kiu/eAVR/eAVR6-adapter-hrz/eAVR6-adapter-hrz2.png

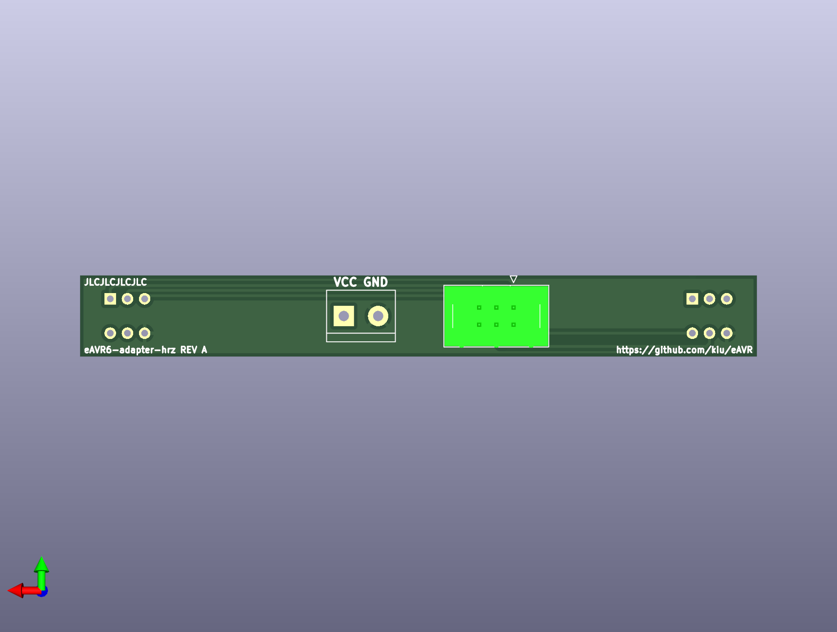
eAVR6-adapter-hrz/eAVR6-adapter-hrz2.png
