kiu/eAVR/eAVR6-example/eAVR6-example2.png

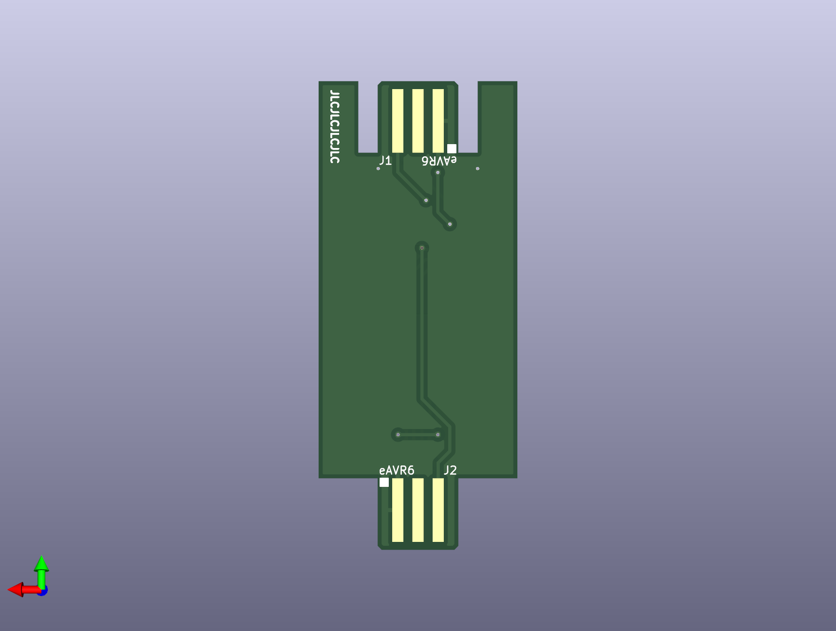
eAVR6-example/eAVR6-example2.png
