kiu/eAVR/eAVR6-UPDI-adapter/eAVR6-UPDI-adapter2.png

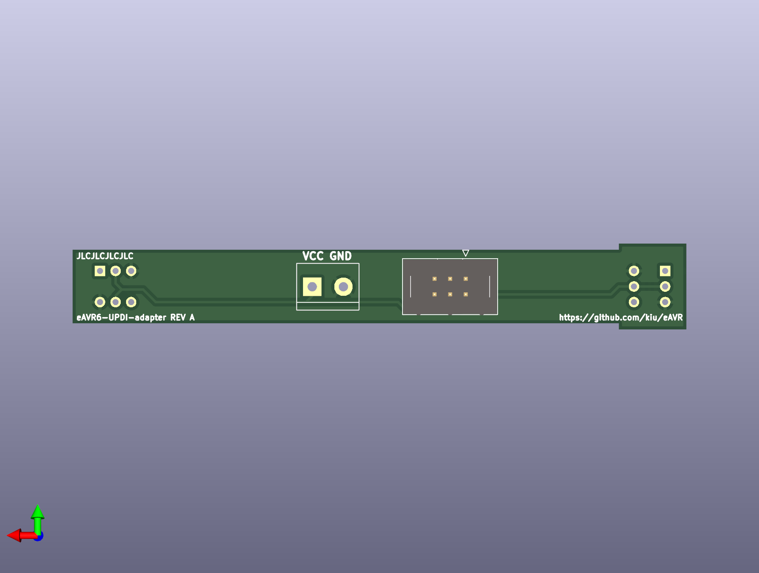
eAVR6-UPDI-adapter/eAVR6-UPDI-adapter2.png
