kiu/eAVR/eAVR6-UPDI-example/eAVR6-UPDI-example2.png

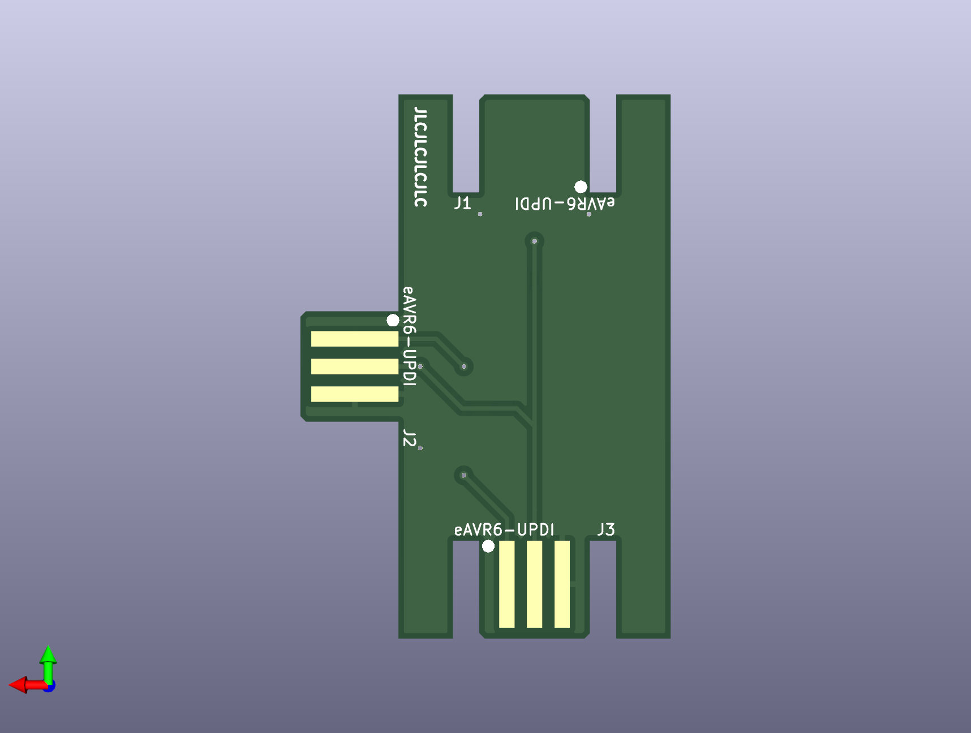
eAVR6-UPDI-example/eAVR6-UPDI-example2.png
