kiu/eAVR/eAVR6-UPDI-example/eAVR6-UPDI-example.png

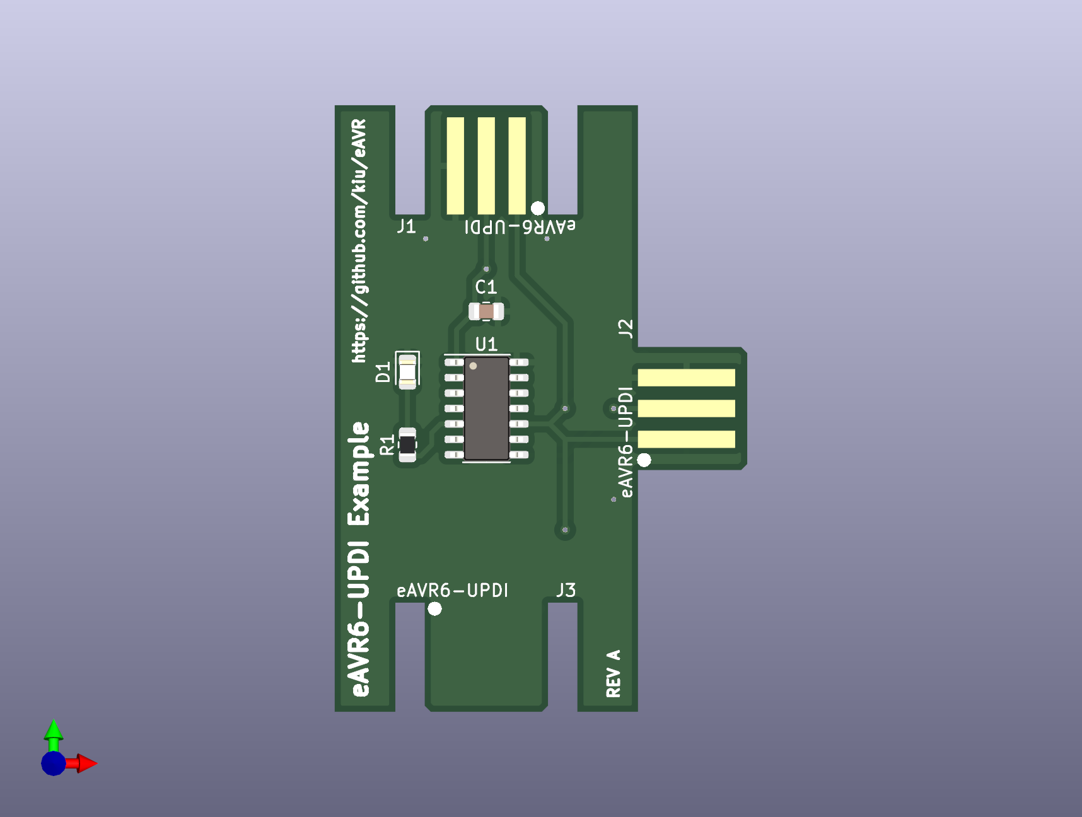
eAVR6-UPDI-example/eAVR6-UPDI-example.png
